mgoodfellow/espuino-boxes/case/first-pass/rough-box-corner.png

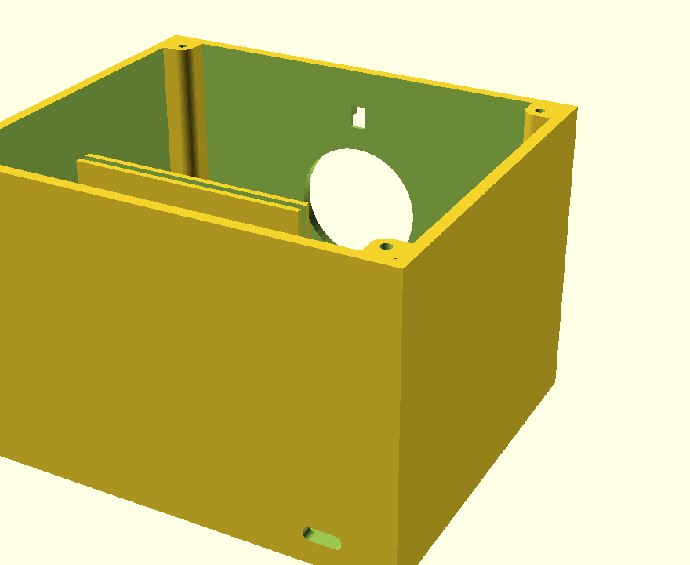
case/first-pass/rough-box-corner.png
