mgoodfellow/espuino-boxes/case/first-pass/rough-box-coupon.png

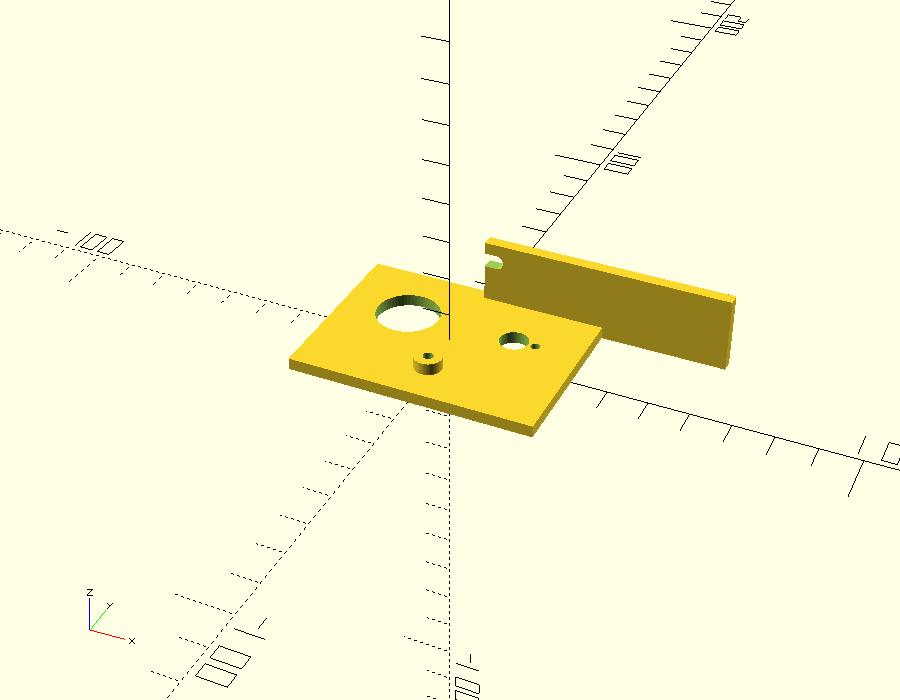
case/first-pass/rough-box-coupon.png
