mgoodfellow/espuino-boxes/case/first-pass/rough-box-cover.png

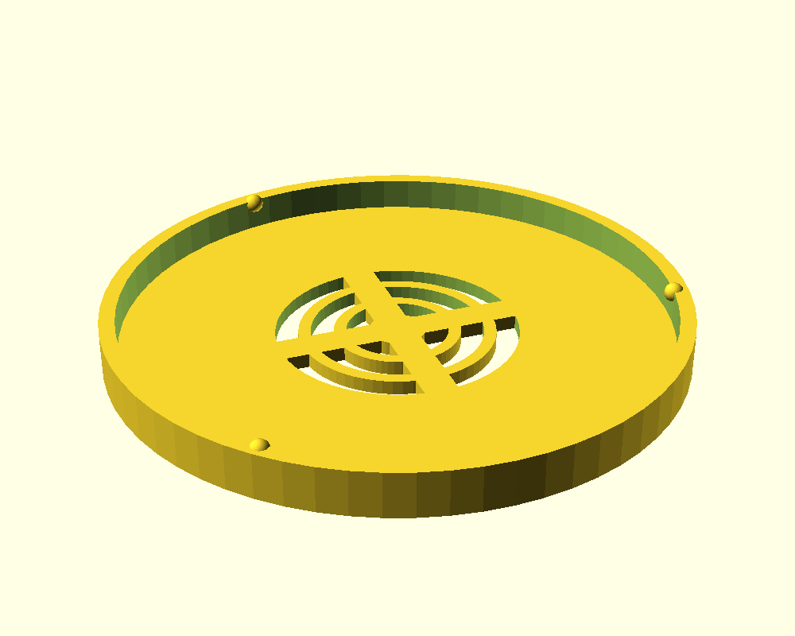
case/first-pass/rough-box-cover.png
