mgoodfellow/espuino-boxes/case/first-pass/rough-box-floor.png

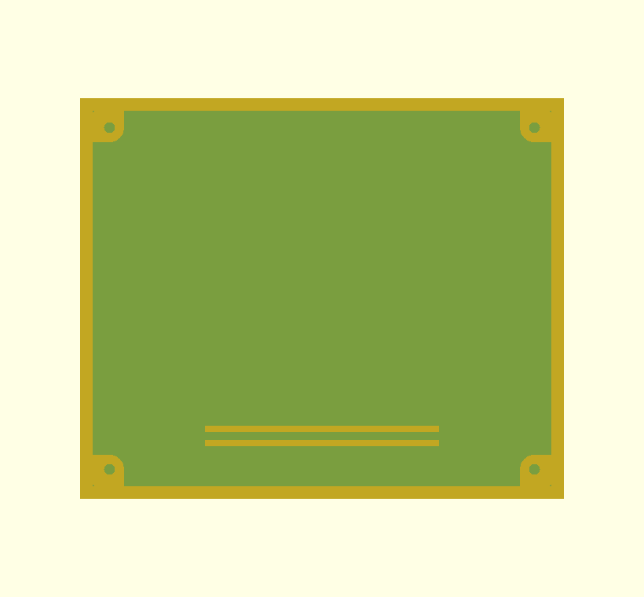
case/first-pass/rough-box-floor.png
