mgoodfellow/espuino-boxes/case/first-pass/rough-box-front.png

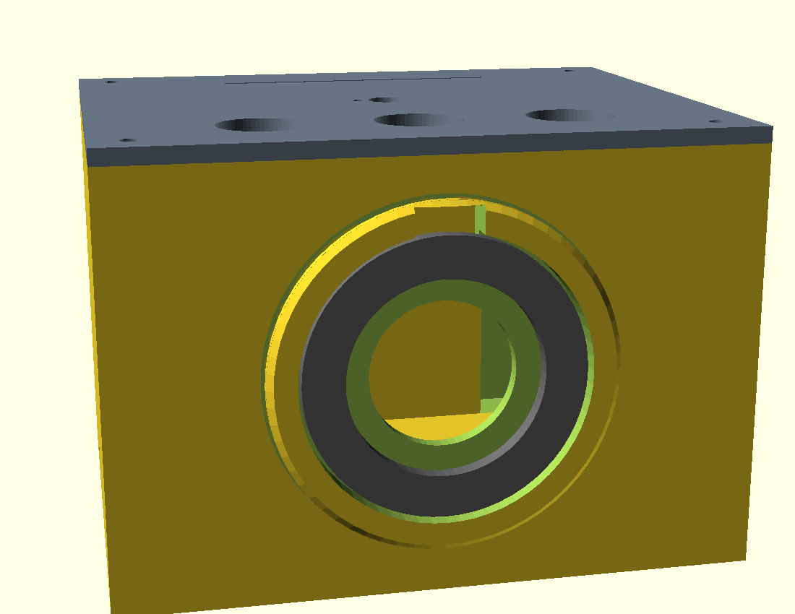
case/first-pass/rough-box-front.png
