mgoodfellow/espuino-boxes/case/first-pass/rough-box-layout-v1.png

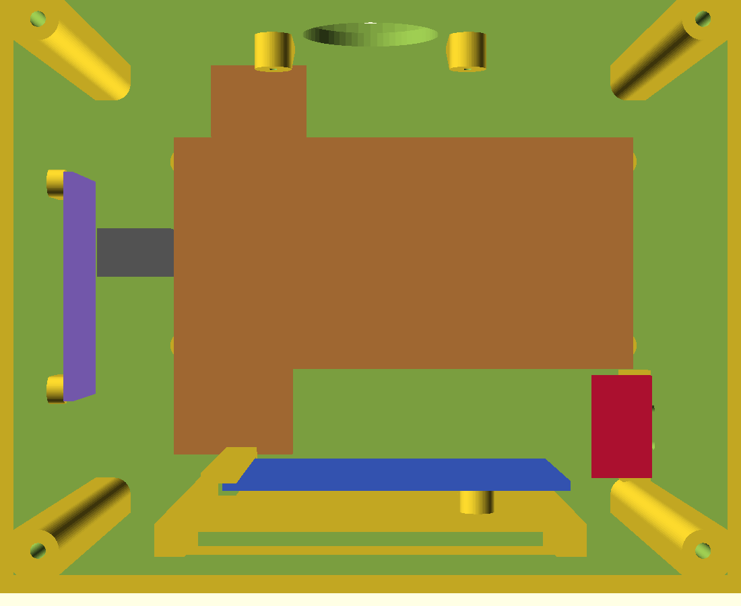
case/first-pass/rough-box-layout-v1.png
