mgoodfellow/espuino-boxes/case/first-pass/rough-box-mounts.png

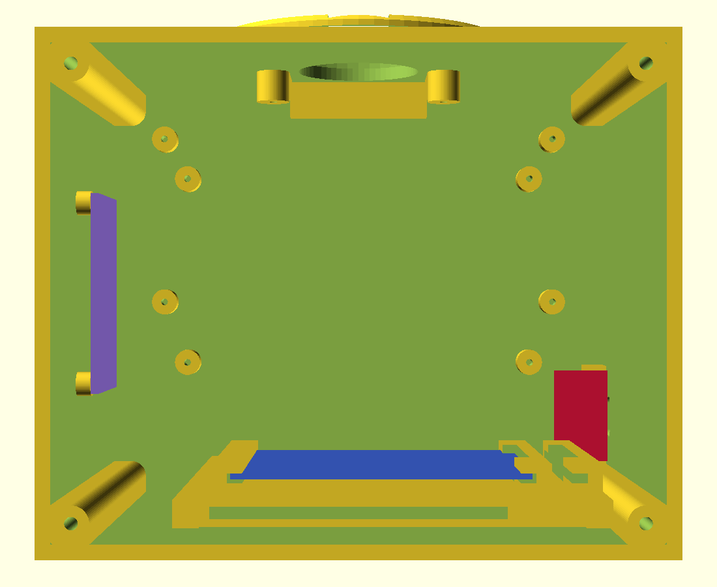
case/first-pass/rough-box-mounts.png
