mgoodfellow/espuino-boxes/case/first-pass/rough-box-rear.png

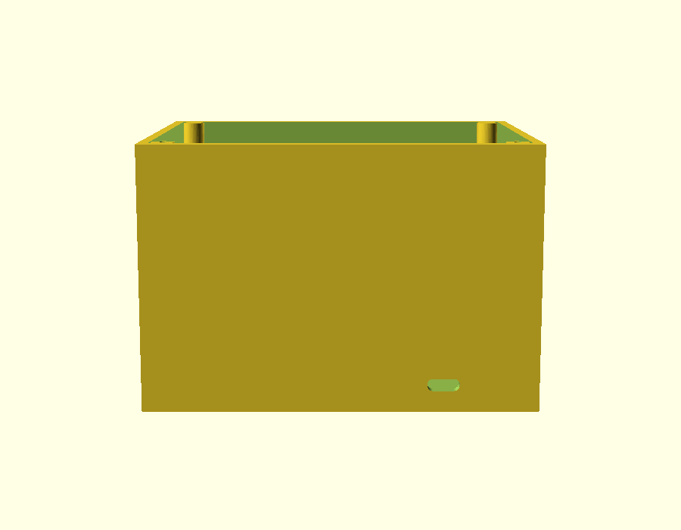
case/first-pass/rough-box-rear.png
