mgoodfellow/espuino-boxes/case/first-pass/rough-box-shell-front.png

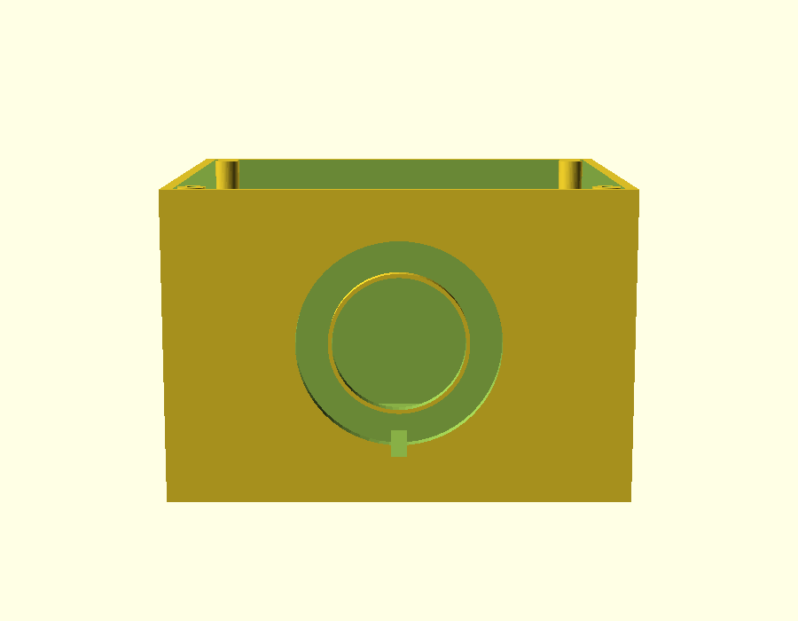
case/first-pass/rough-box-shell-front.png
