mgoodfellow/espuino-boxes/case/first-pass/rough-box-speaker-mount.png

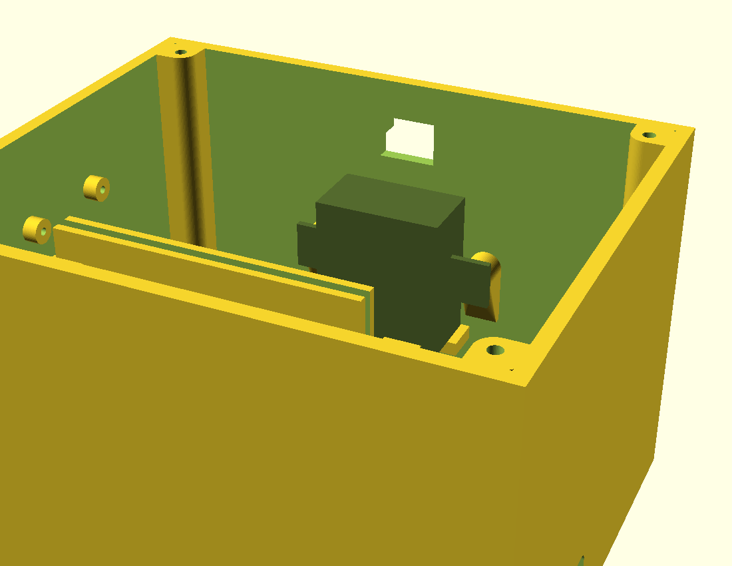
case/first-pass/rough-box-speaker-mount.png
