mgoodfellow/espuino-boxes/case/first-pass/rough-box-top.png

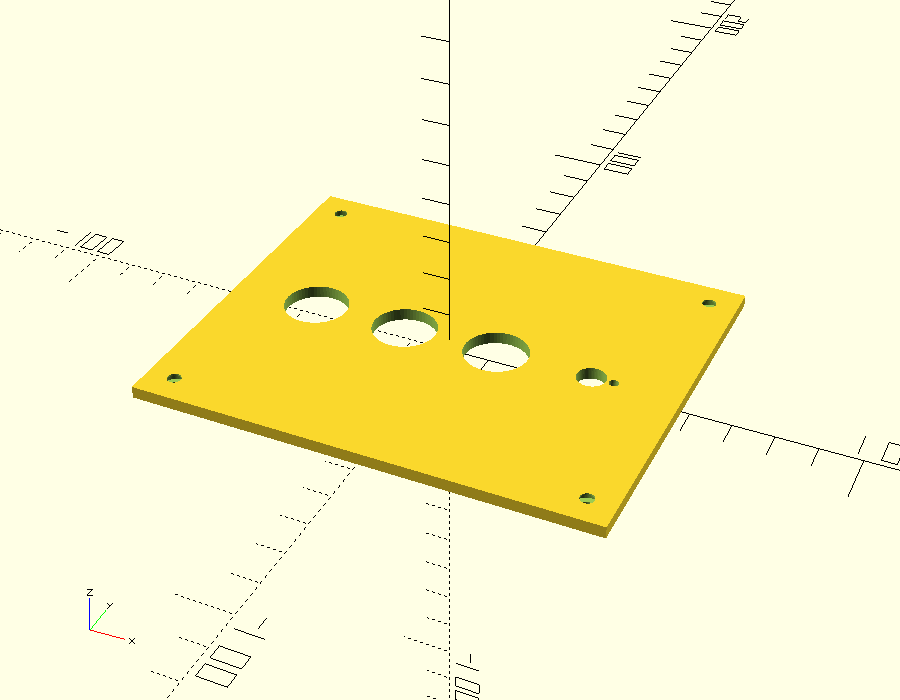
case/first-pass/rough-box-top.png
