mgoodfellow/espuino-boxes/case/first-pass/rough-box-usb3d.png

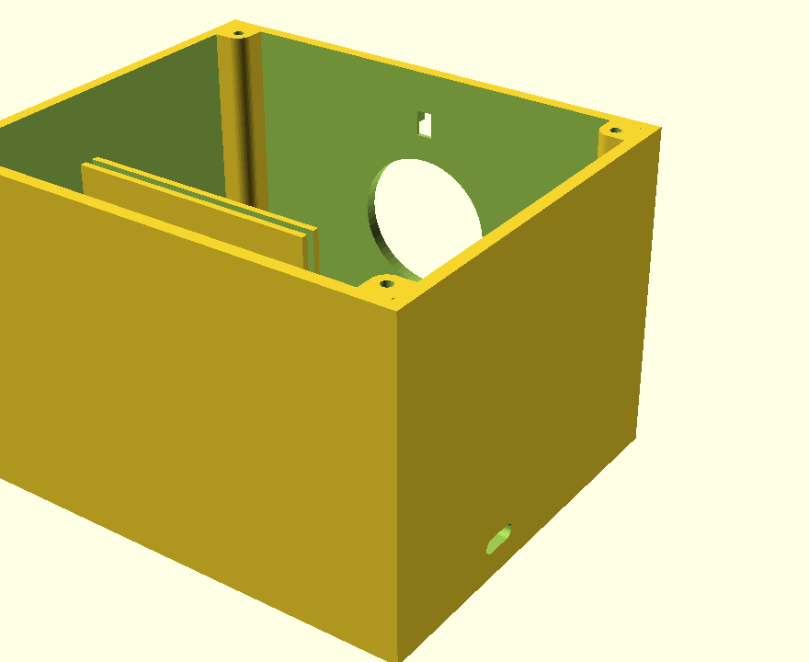
case/first-pass/rough-box-usb3d.png
