mgoodfellow/espuino-boxes/case/first-pass/rough-box-usbfit.png

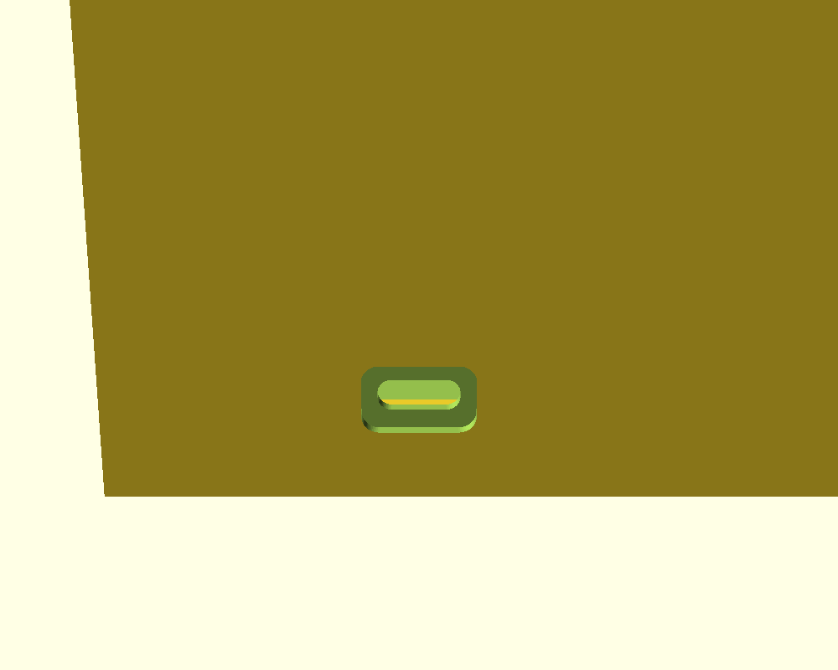
case/first-pass/rough-box-usbfit.png
